Hypernova-Oy/emb-toveri/Blender/untitled.png

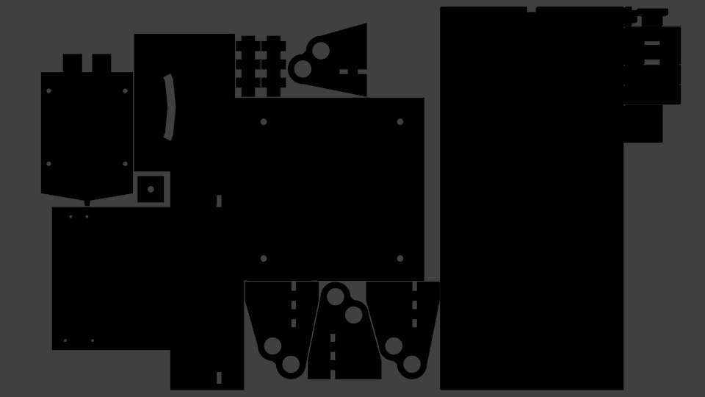
Blender/untitled.png
