Hypernova-Oy/emb-toveri/Documents/WGC300USB_config.png

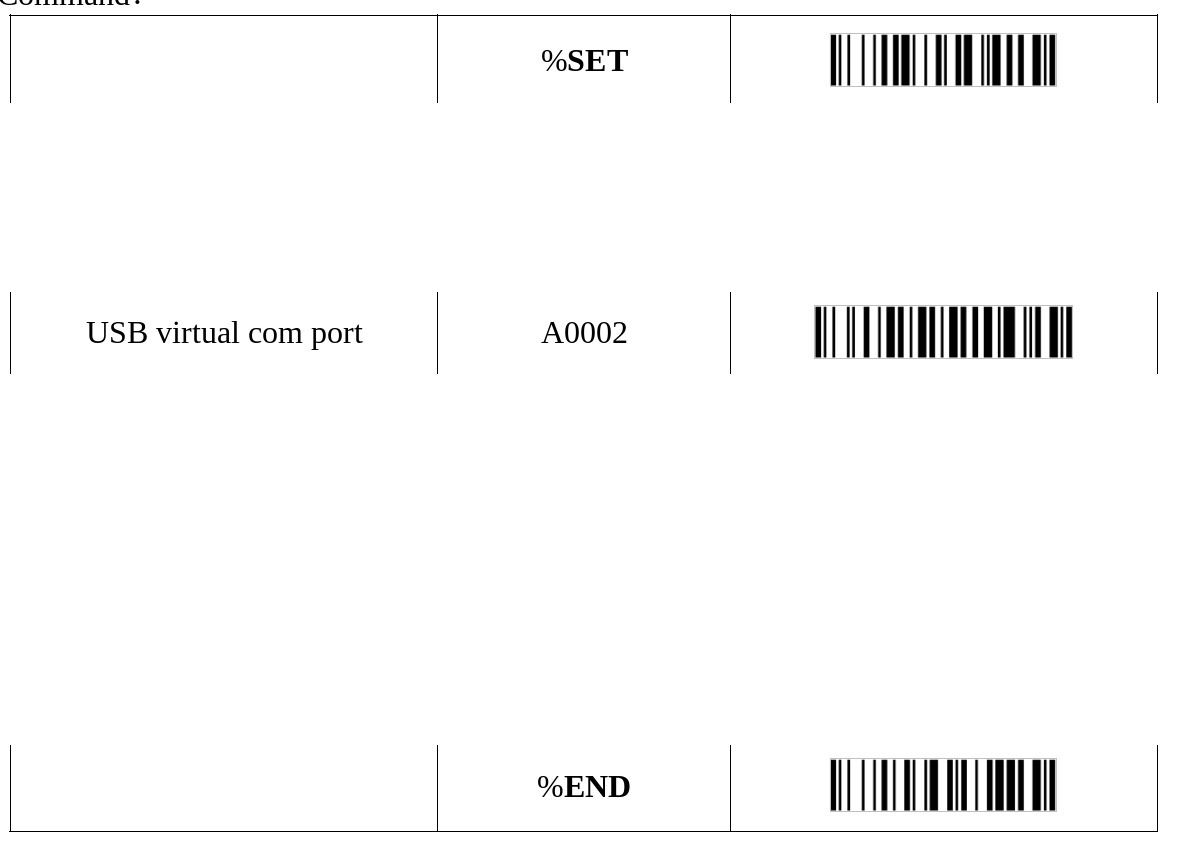
Documents/WGC300USB_config.png
