Hypernova-Oy/emb-toveri/Pictures/Enclosures/blue_acrylic_front.jpg

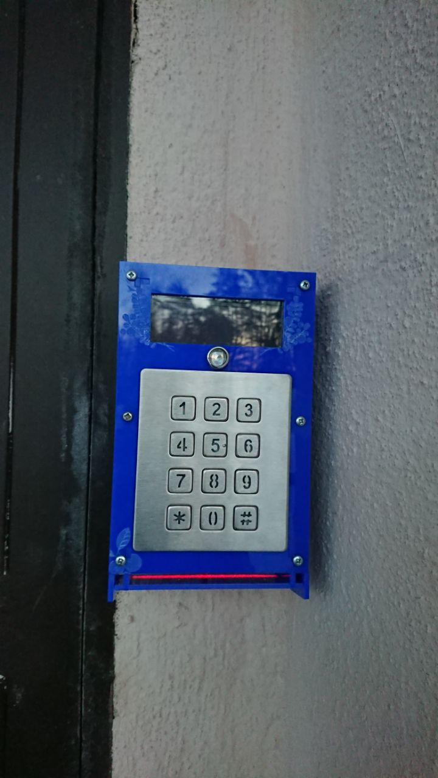
Pictures/Enclosures/blue_acrylic_front.jpg
