Hypernova-Oy/emb-toveri/Pictures/Enclosures/blue_acrylic_side_engraving.jpg

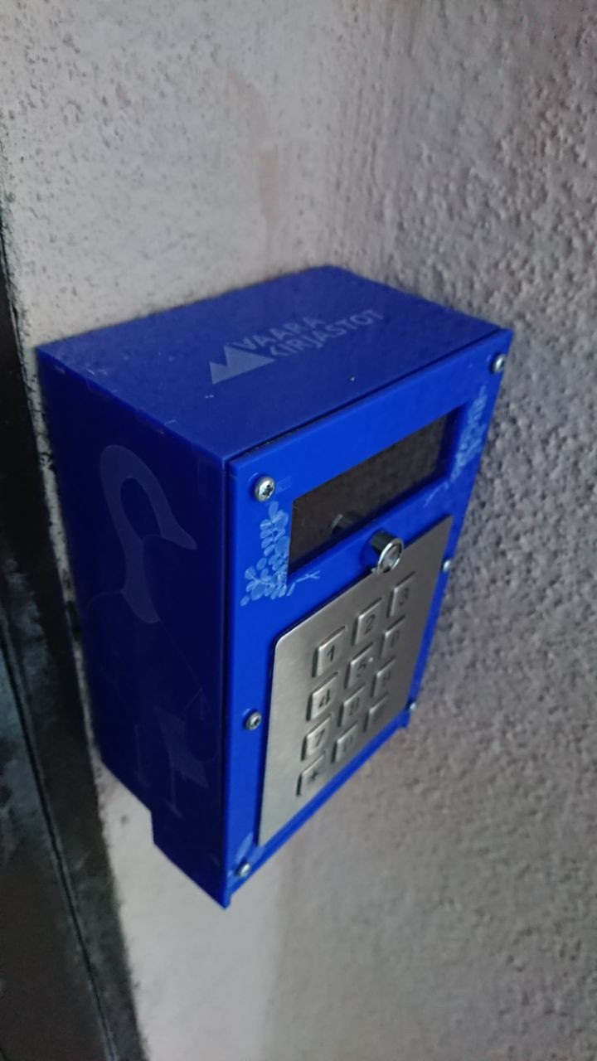
Pictures/Enclosures/blue_acrylic_side_engraving.jpg
