Hypernova-Oy/emb-toveri/Pictures/Enclosures/blue_acrylic_side_sticker.jpg

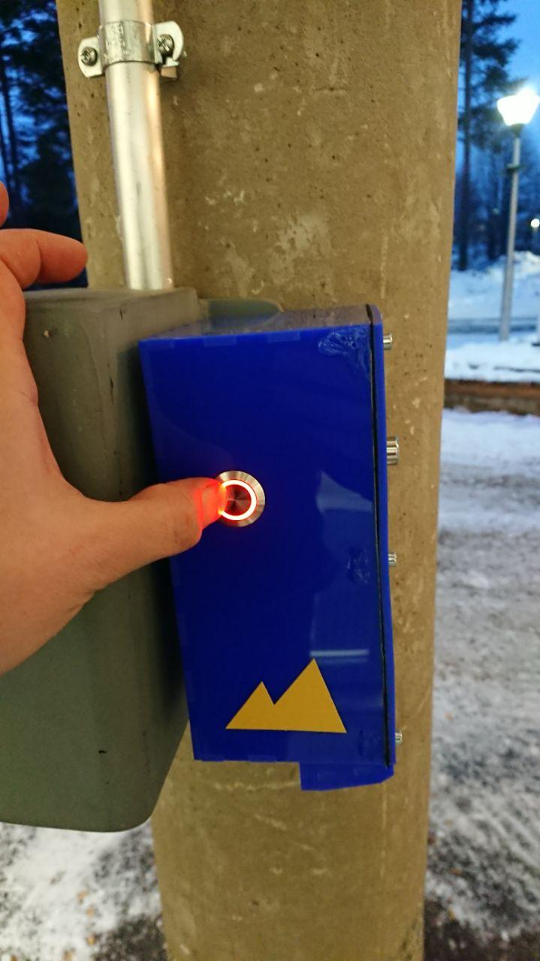
Pictures/Enclosures/blue_acrylic_side_sticker.jpg
