Hypernova-Oy/emb-toveri/Pictures/Enclosures/blue_acrylic_top_engraving.jpg

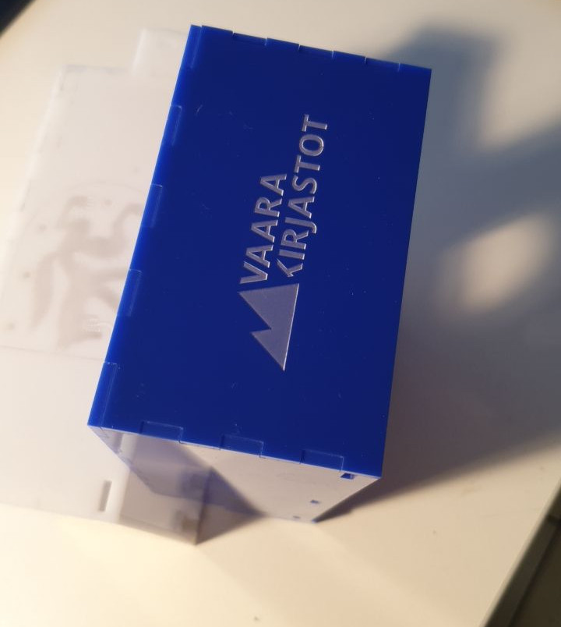
Pictures/Enclosures/blue_acrylic_top_engraving.jpg
