Hypernova-Oy/emb-toveri/Pictures/Enclosures/gold_acrylic_tree_front.jpg

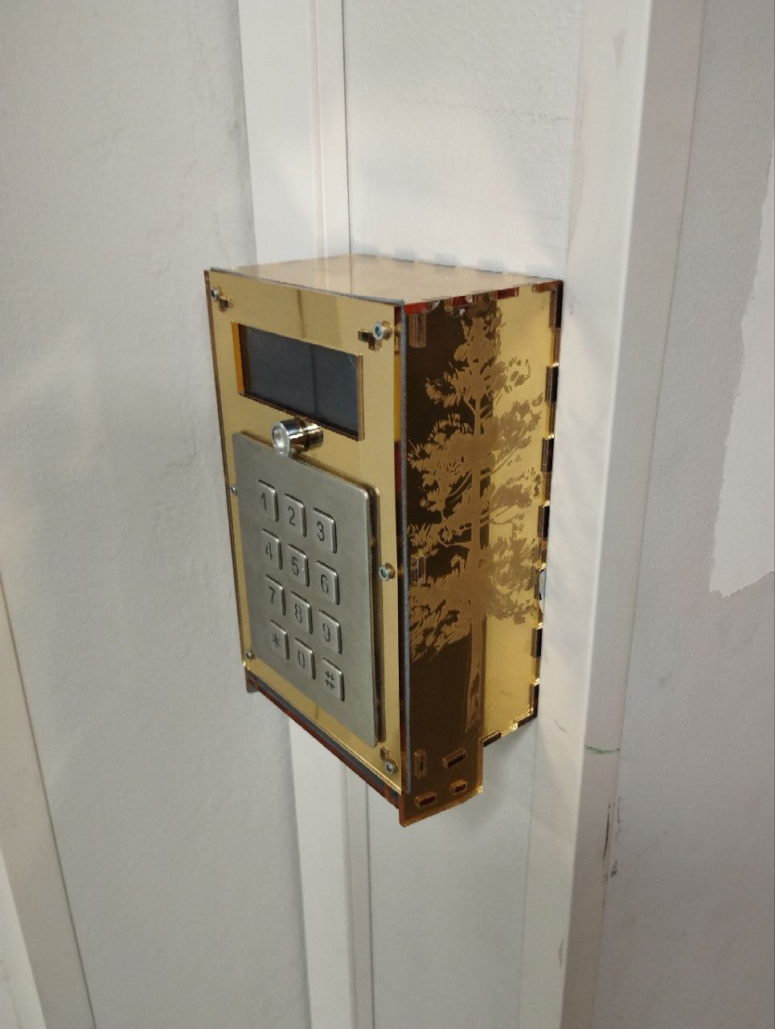
Pictures/Enclosures/gold_acrylic_tree_front.jpg
