Hypernova-Oy/emb-toveri/Pictures/Enclosures/internal_enclosure_1.jpg

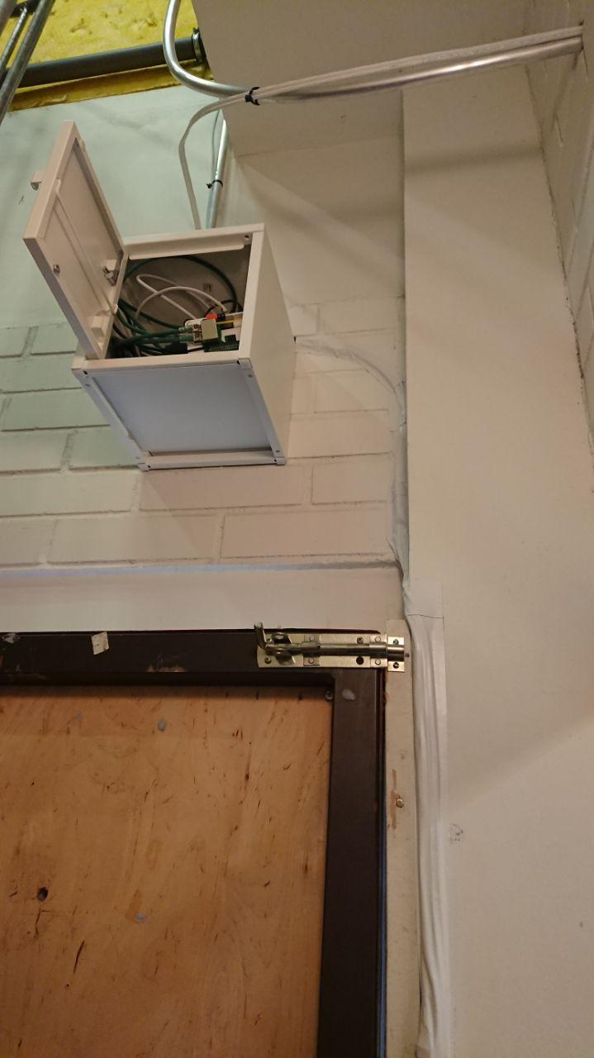
Pictures/Enclosures/internal_enclosure_1.jpg
