Hypernova-Oy/emb-toveri/Pictures/Enclosures/internal_enclosure_2.jpg

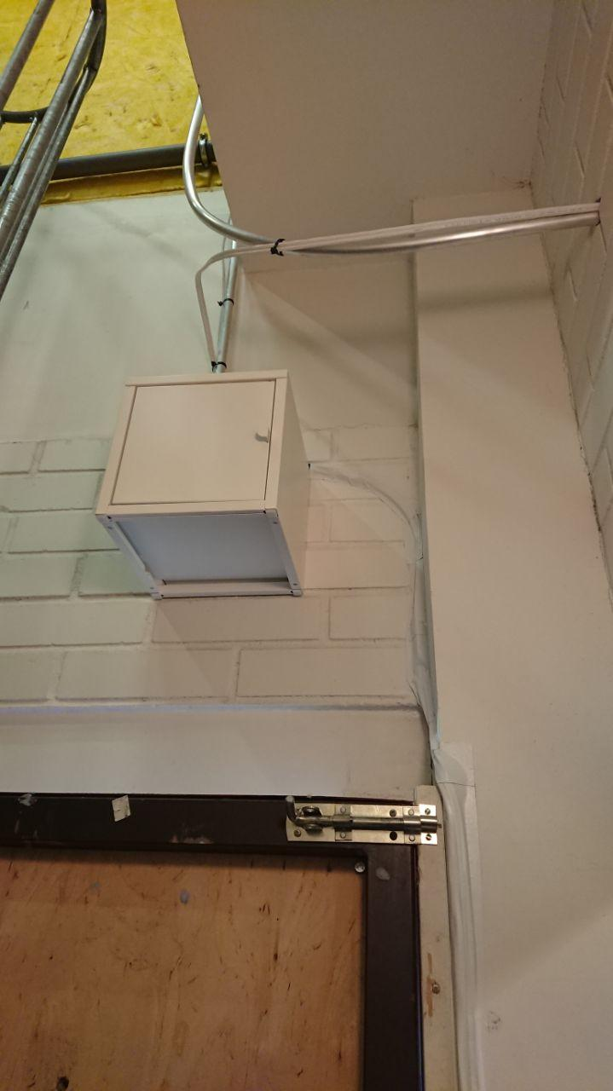
Pictures/Enclosures/internal_enclosure_2.jpg
