Hypernova-Oy/emb-toveri/Pictures/Enclosures/matte_black_front.jpg

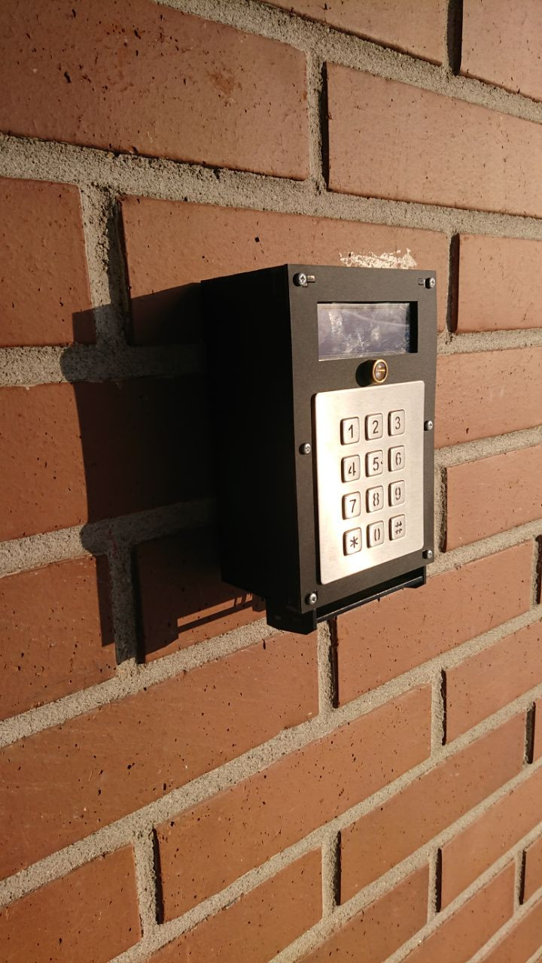
Pictures/Enclosures/matte_black_front.jpg
