Hypernova-Oy/emb-toveri/Pictures/Enclosures/matte_gray_free_vector_graphics.jpg

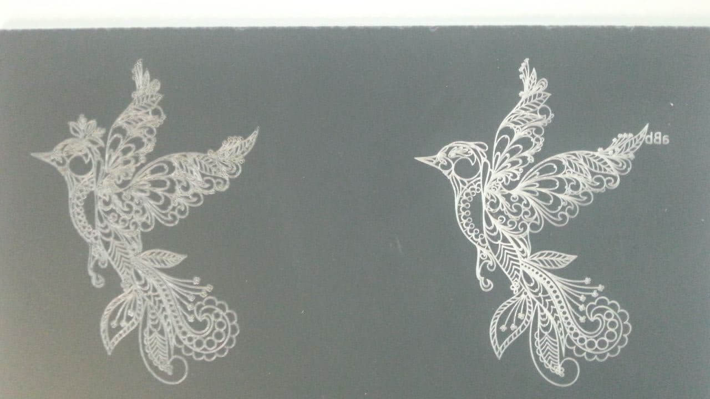
Pictures/Enclosures/matte_gray_free_vector_graphics.jpg
