Hypernova-Oy/emb-toveri/Pictures/Enclosures/neon_orange_acrylic_full2_engraving.jpg

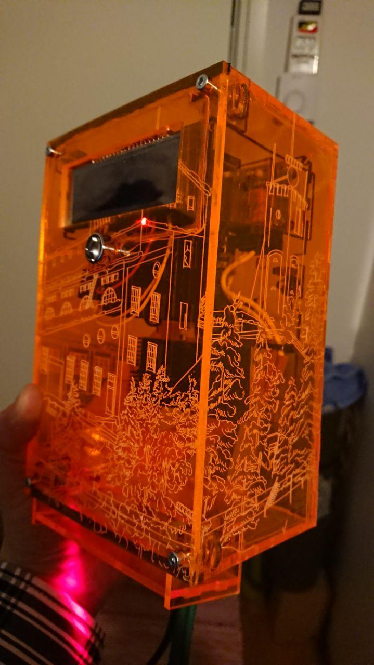
Pictures/Enclosures/neon_orange_acrylic_full2_engraving.jpg
