Hypernova-Oy/emb-toveri/Pictures/Enclosures/neon_orange_acrylic_full_engraving.jpg

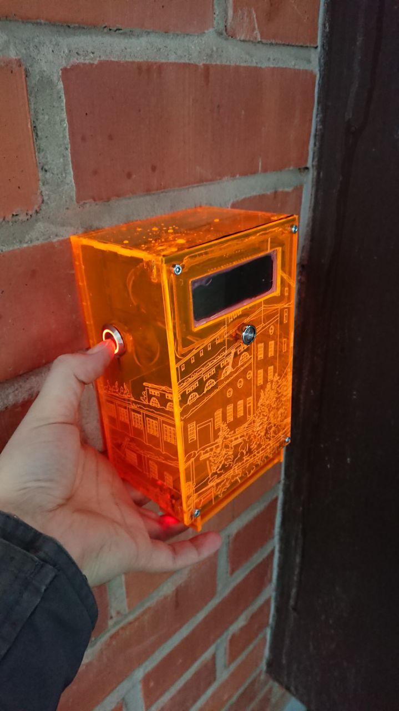
Pictures/Enclosures/neon_orange_acrylic_full_engraving.jpg
