Hypernova-Oy/emb-toveri/Pictures/Enclosures/pink-glitter-unicorn.jpg

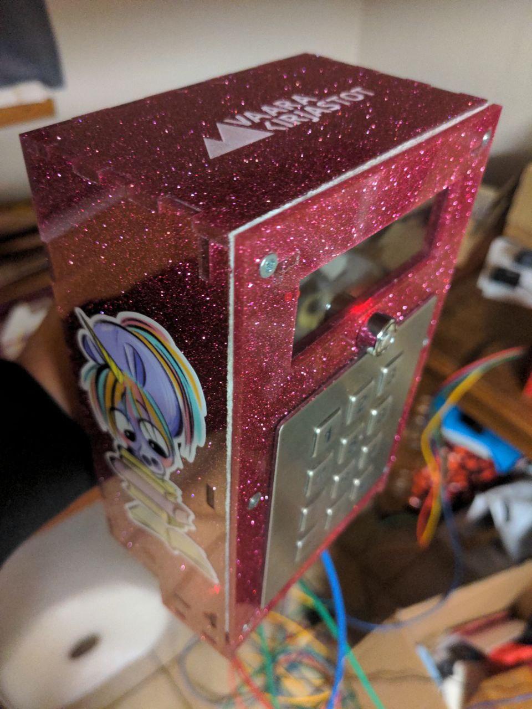
Pictures/Enclosures/pink-glitter-unicorn.jpg
