Hypernova-Oy/emb-toveri/Pictures/Enclosures/red-colibri.jpg

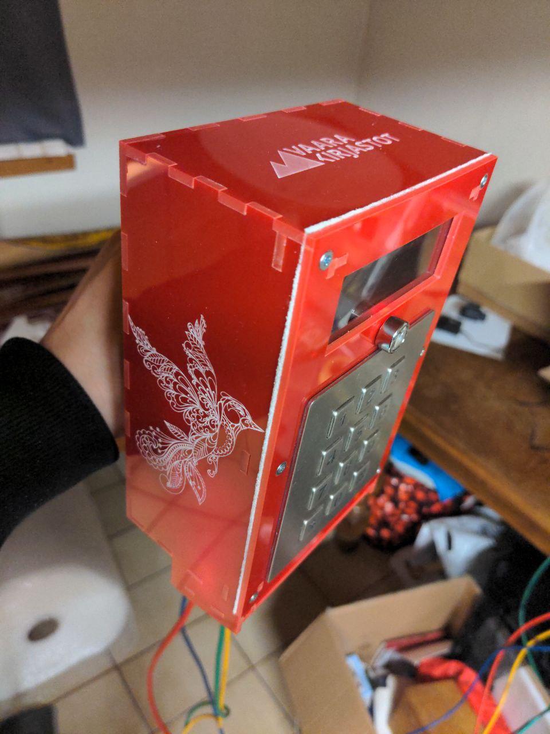
Pictures/Enclosures/red-colibri.jpg
