Hypernova-Oy/emb-toveri/Pictures/Enclosures/red_acrylic_side_engraving.jpg

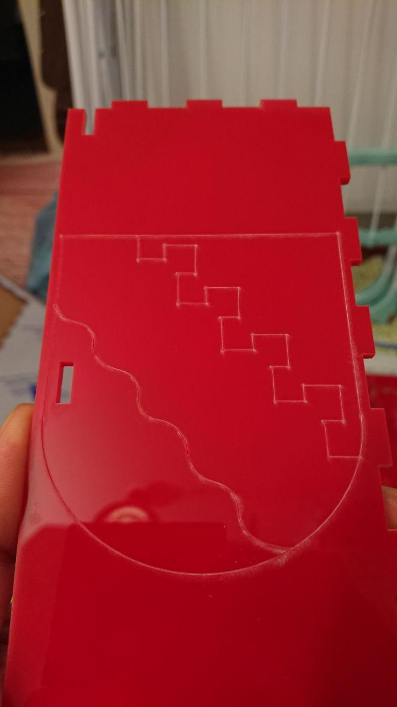
Pictures/Enclosures/red_acrylic_side_engraving.jpg
