Hypernova-Oy/emb-toveri/Pictures/Enclosures/white28%_acrylic_front.jpg

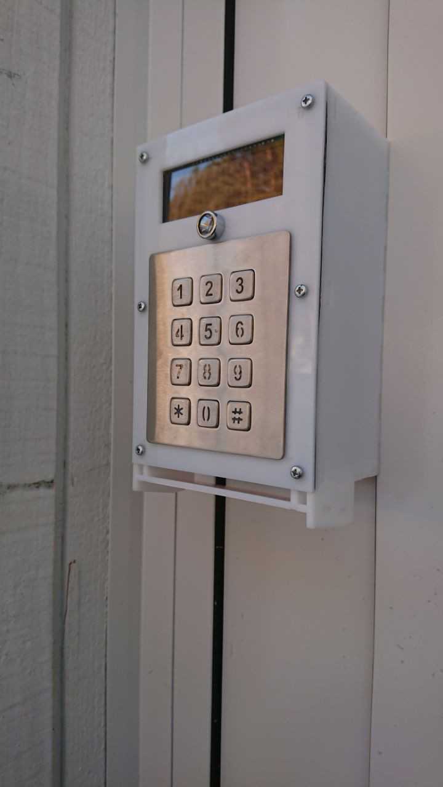
Pictures/Enclosures/white28%_acrylic_front.jpg
