Hypernova-Oy/emb-toveri/Pictures/Enclosures/white28%_acrylic_side_wolf.jpg

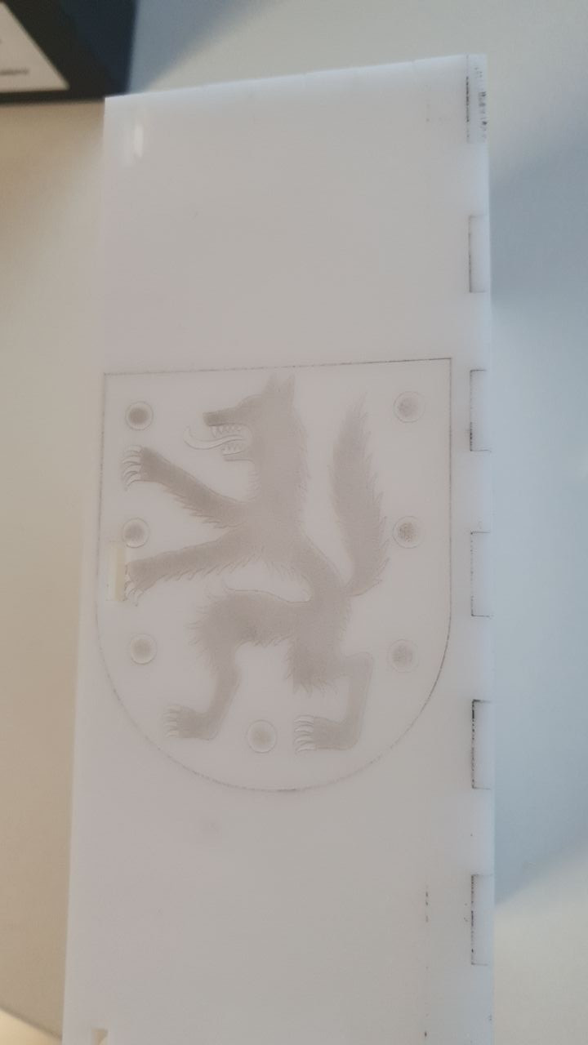
Pictures/Enclosures/white28%_acrylic_side_wolf.jpg
