Hypernova-Oy/emb-toveri/Pictures/Interior enclosure/Rasbperry_enclosure_top.png

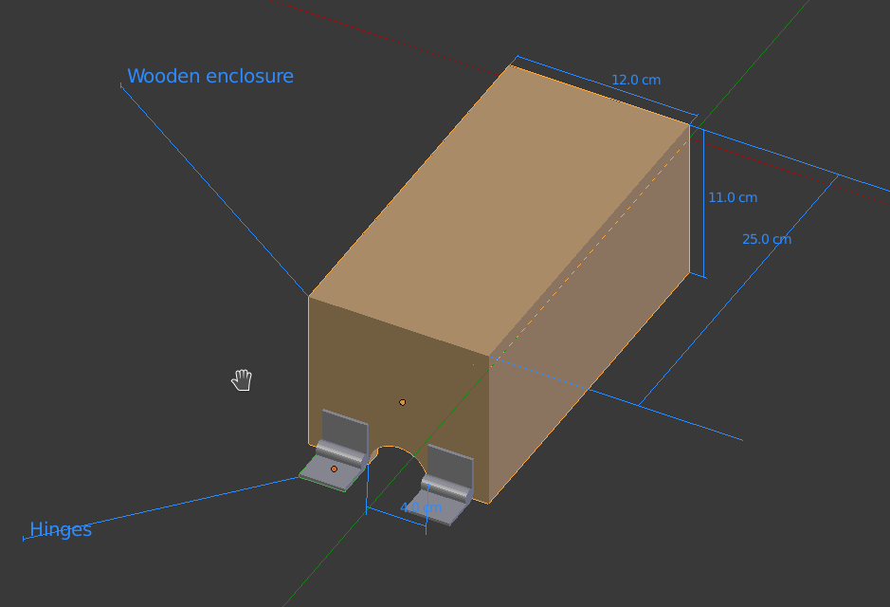
Pictures/Interior enclosure/Rasbperry_enclosure_top.png
