Hypernova-Oy/emb-toveri/Pictures/Interior enclosure/Raspberry_enclosure_bottom.png

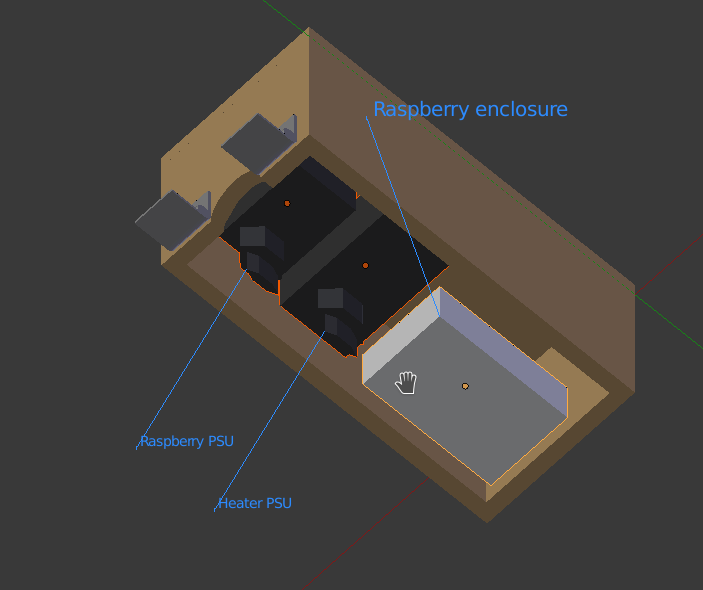
Pictures/Interior enclosure/Raspberry_enclosure_bottom.png
