Hypernova-Oy/emb-toveri/Pictures/Interior enclosure/Raspberry_enclosure_bottom_wire.png

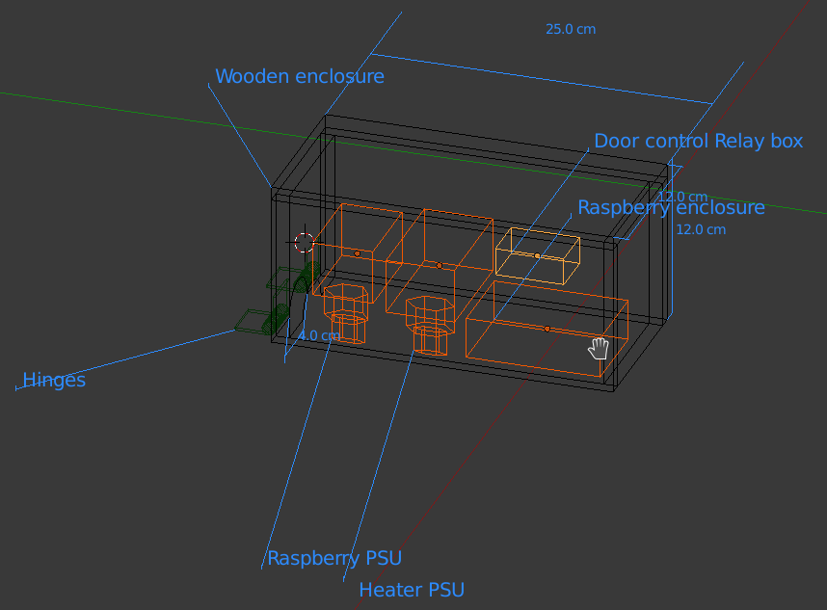
Pictures/Interior enclosure/Raspberry_enclosure_bottom_wire.png
