Hypernova-Oy/emb-toveri/Pictures/matte_black_full_engraving.jpg

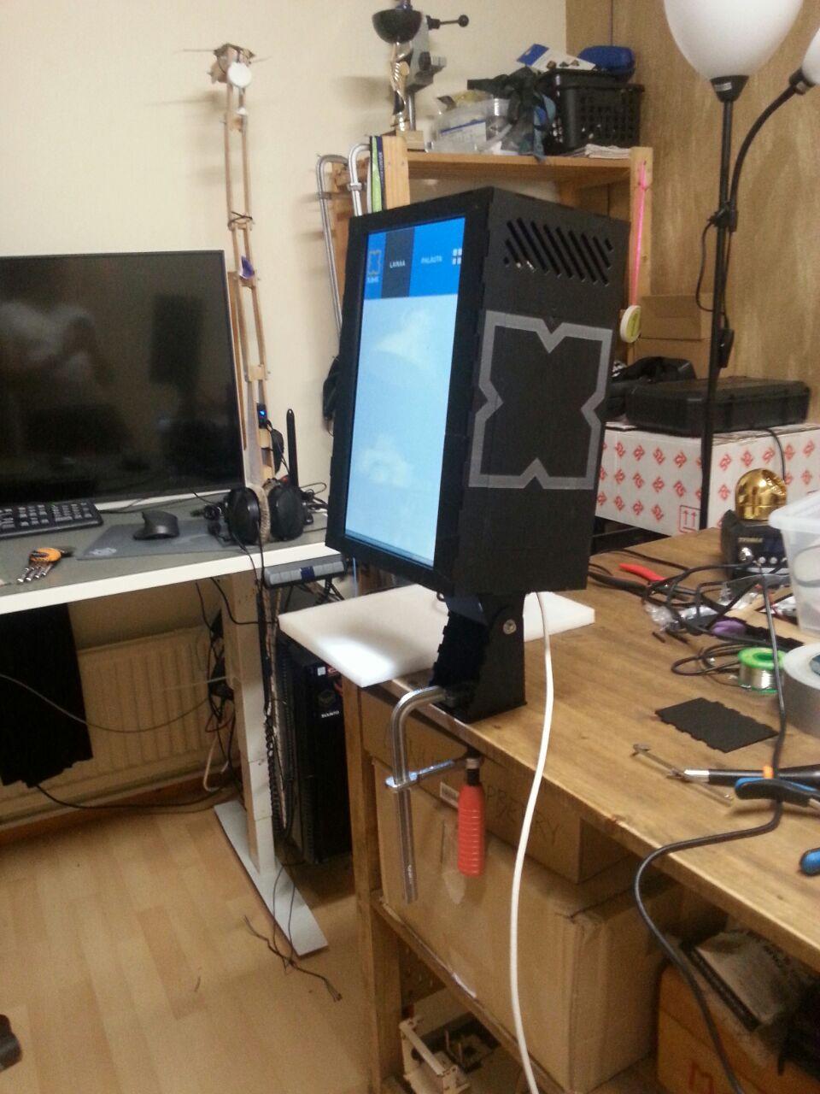
Pictures/matte_black_full_engraving.jpg
