Hypernova-Oy/emb-toveri/Pictures/matte_gray_full_engraving.jpg

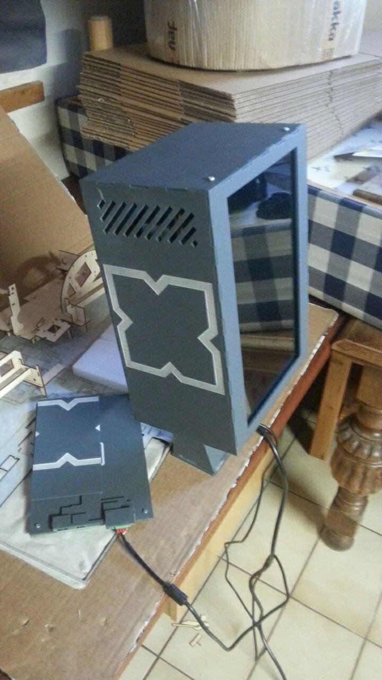
Pictures/matte_gray_full_engraving.jpg
