Hypernova-Oy/emb-toveri/Pictures/red_full_engraving.jpg

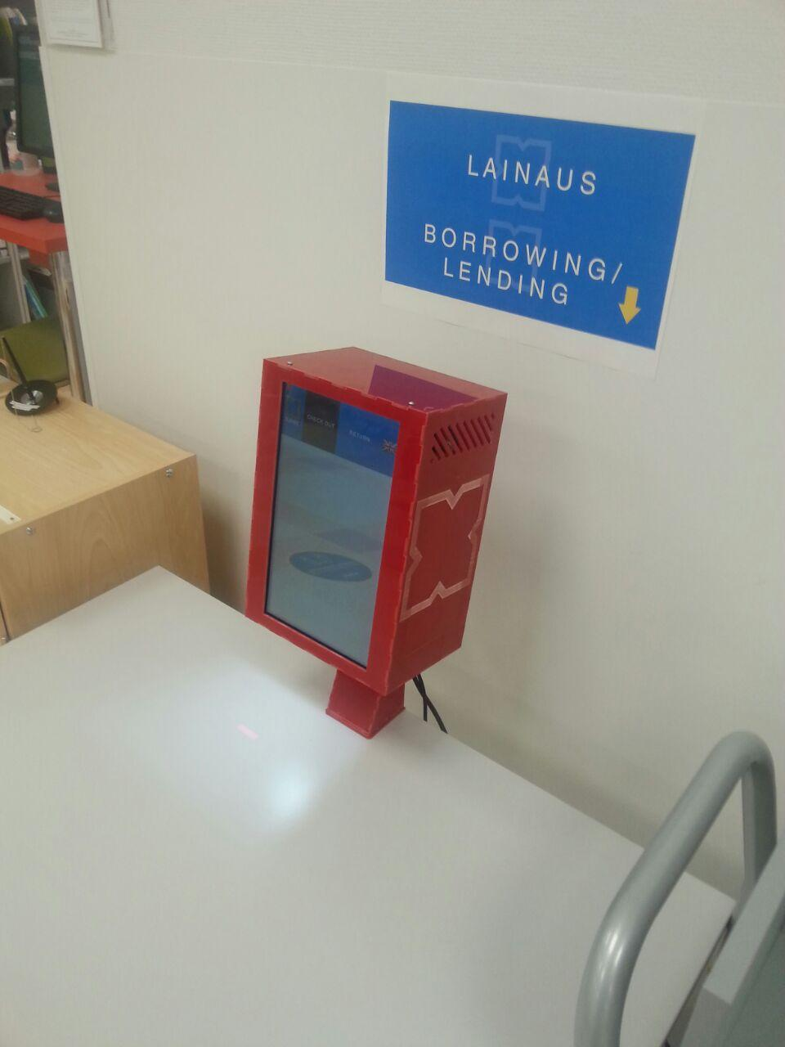
Pictures/red_full_engraving.jpg
