Hypernova-Oy/emb-toveri/Documents/barcodeReaderManualConfigurationCodes.png

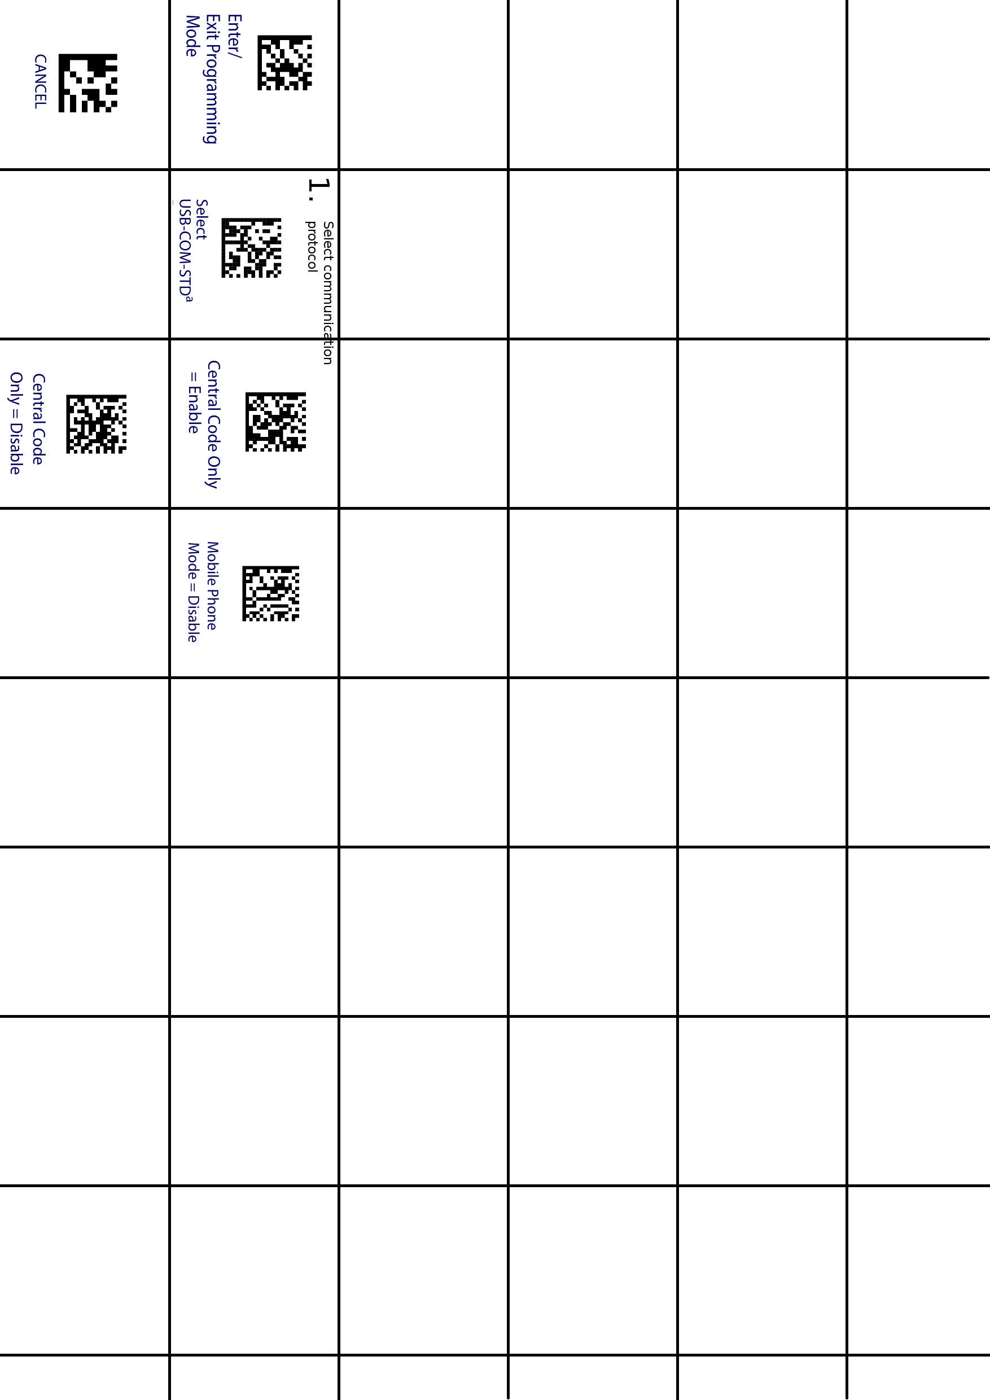
Documents/barcodeReaderManualConfigurationCodes.png
