Hypernova-Oy/emb-toveri/Pictures/Assembled/Eno.jpg

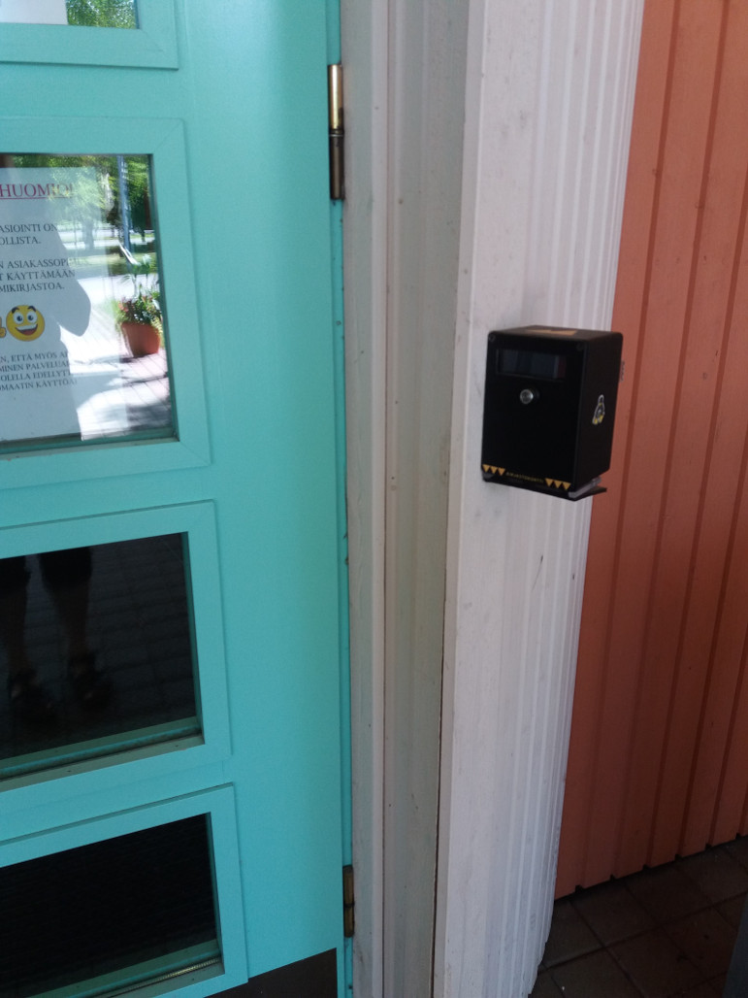
Pictures/Assembled/Eno.jpg
