Hypernova-Oy/emb-toveri/Pictures/Assembled/toveri_bottom+card.jpg

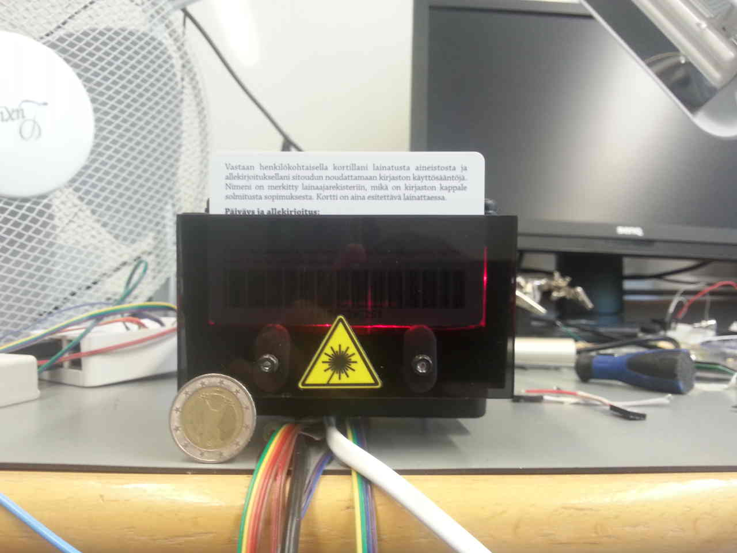
Pictures/Assembled/toveri_bottom+card.jpg
