Hypernova-Oy/emb-toveri/Pictures/Assembled/toveri_bottom.jpg

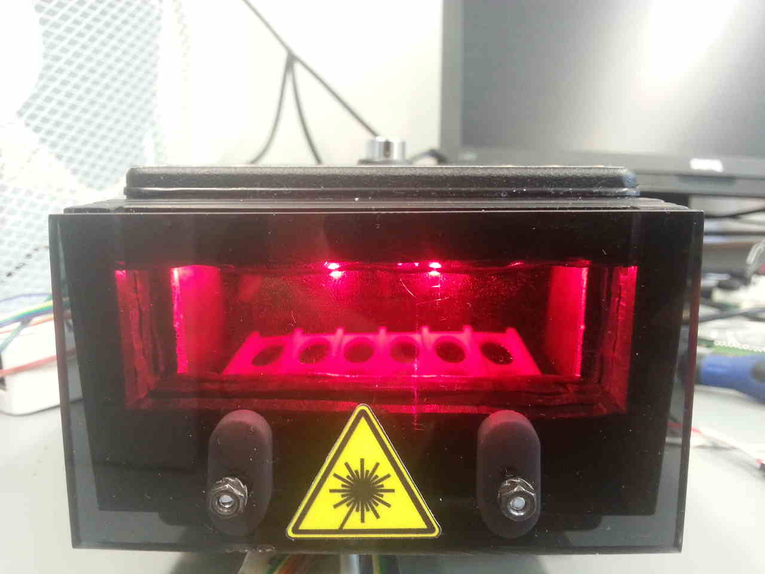
Pictures/Assembled/toveri_bottom.jpg
